ak66666/ThumbsUpV11_5x12_KailhChoc_MX_ProMicro/Photos/IMG_20250605_153905951.jpg

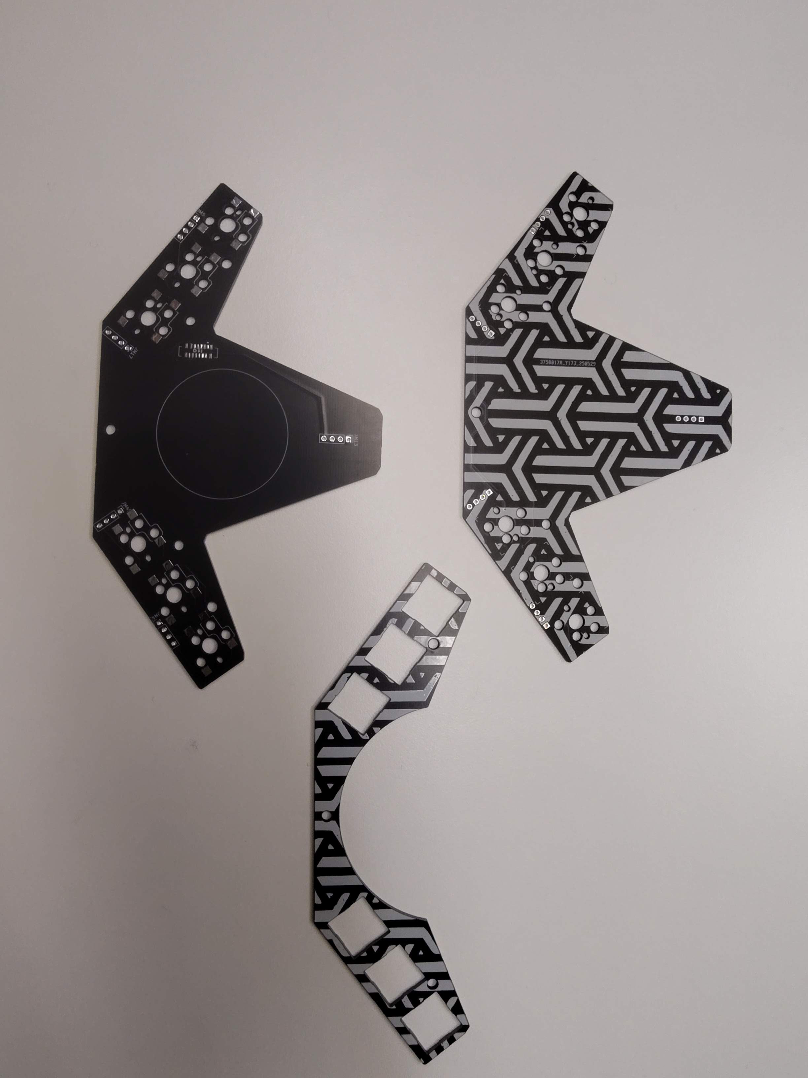
Photos/IMG_20250605_153905951.jpg
