ak66666/ThumbsUpV11_5x12_KailhChoc_MX_ProMicro/Photos/IMG_20250605_222035120_HDR.jpg

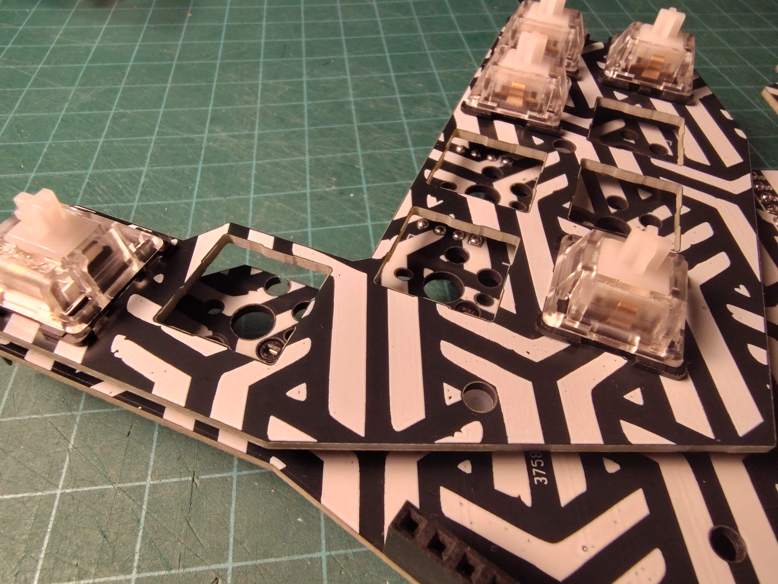
Photos/IMG_20250605_222035120_HDR.jpg
