ak66666/ThumbsUpV11_5x12_KailhChoc_MX_ProMicro/Photos/IMG_20250606_115900263.jpg

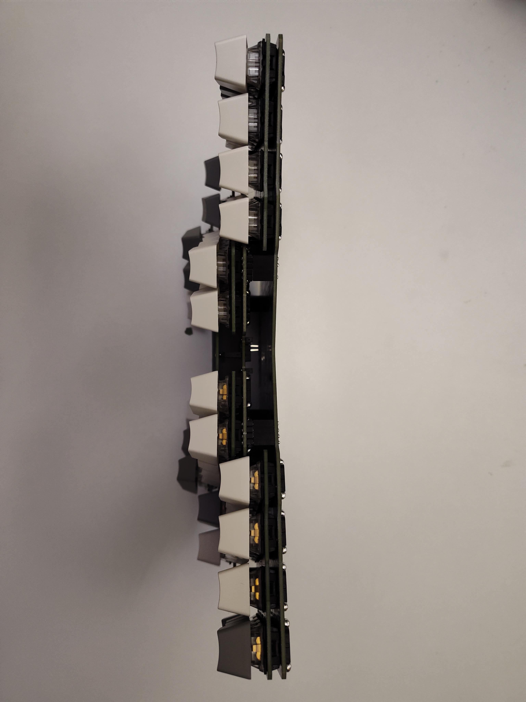
Photos/IMG_20250606_115900263.jpg
